uli-pi/MC-CPM-Computer-Clone/FLO-80/FLO-80.jpg

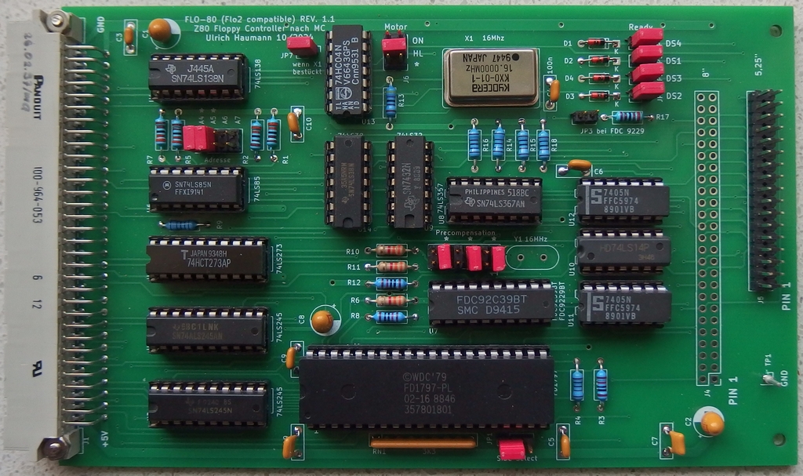
FLO-80/FLO-80.jpg
